technobly/parti-badge/firmware/src/music/xmassongs.h

/*
 *      Copyright 2017 Particle Industries, Inc.
 * 
 *      Originally created for the Particle Christmas Tree Shield: 
 *       https://github.com/particle-iot/xmastree. Modified to add Particle
 *      Mesh publish for netowrked light displays.
 *
 *      Licensed under the Apache License, Version 2.0 (the "License");
 *      you may not use this file except in compliance with the License.
 *      You may obtain a copy of the License at
 *
 *          http://www.apache.org/licenses/LICENSE-2.0
 *
 *      Unless required by applicable law or agreed to in writing, software
 *      distributed under the License is distributed on an "AS IS" BASIS,
 *      WITHOUT WARRANTIES OR CONDITIONS OF ANY KIND, either express or implied.
 *      See the License for the specific language governing permissions and
 *      limitations under the License.
 *
 */
#include "macros.h"

#define SONG_COUNT 5

#define SONG_JOYTOTHEWORLD 0
#define SONG_WEWHISHYOUAMERRYXMAS 1
#define SONG_RUDOLFTHEREDNOSEDREINDEER 2
#define SONG_JINGLEBELLS 3
#define SONG_SILENTNIGHT 4

#define Do 523 / 2
#define Do_ 1046 / 2
#define Re 587 / 2
#define Re_ 1175 / 2
#define Mi 659 / 2
#define Mi_ 1318 / 2
#define Fa 698 / 2
#define Fa_ 1397 / 2
#define So 784 / 2
#define La 880 / 2
#define Si 988 / 2
#define _Si 494 / 2
#define _La 440 / 2
#define _So 392 / 2

#define bt 323
#define bt2 bt * 2
#define bt3 bt * 3
#define bt6 bt * 6
#define bt1_2 bt / 2
#define bt3_2 (bt / 2) * 3
#define bt1_4 bt / 4

/*
 *      Credit:
 *          Midi to Arduino Converter
 *              - Andy Tran (extramaster), 2015
 *          https://www.extramaster.net/tools/midiToArduino/
 *
 *      The songs are generated from:
 *          https://www.extramaster.net/tools/midiToArduino/processFile/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
 *          https://www.extramaster.net/tools/midiToArduino/processFile/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
 *          https://www.extramaster.net/tools/midiToArduino/processFile/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
 *          https://www.extramaster.net/tools/midiToArduino/processFile/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
 */

/* Song List */
String songList = "Joy To The World, We Wish You A Merry Xmas, Rudolf the Red Nosed Reindeer, Jingle Bells, Silent Night";

/* An indicator to exit the current song */
bool changeSong = false;

bool delaySong(unsigned duration)
{
  while (duration > 0 && !changeSong)
  {
    unsigned thisDelay = duration > 100 ? 100 : duration;
    delay(thisDelay);
    duration -= thisDelay;
  }

  return changeSong;
}

/*
 *
 *      Silent Night
 *
 *      More Information:
 *          https://en.wikipedia.org/wiki/Silent_Night
 *
 */

#define NOTE_COUNT_SILENTNIGHT 46

const int notes_silentNight[] = {
    // Note, Duration
    So, bt3_2,
    La, bt1_2,
    So, bt,
    Mi, bt3,

    So, bt3_2,
    La, bt1_2,
    So, bt,
    Mi, bt3,

    Re_, bt2,
    Re_, bt1_2,
    Si, bt3,

    Do_, bt2,
    Do_, bt1_2,
    So, bt3,

    La, bt2,
    La, bt,
    Do_, bt3_2,
    Si, bt1_2,
    La, bt,
    So, bt3_2,
    La, bt1_2,
    So, bt,
    Mi, bt3,

    La, bt2,
    La, bt,
    Do_, bt3_2,
    Si, bt1_2,
    La, bt,
    So, bt3_2,
    La, bt1_2,
    So, bt,
    Mi, bt3,

    Re_, bt2,
    Re_, bt,
    Fa_, bt3_2,
    Re_, bt1_2,
    Si, bt,
    Do_, bt3,

    Mi_, bt3,
    Do_, bt,
    So, bt,
    Mi, bt,
    So, bt3_2,
    Fa, bt1_2,
    Re, bt,
    Do, bt6};

/*
 *
 *      Joy To The World
 *
 *      More information:
 *          https://en.wikipedia.org/wiki/Joy_to_the_World
 *
 */

#define NOTE_COUNT_JOYTOTHEWORLD 57

const float notes_joyToTheWorld[] = {
    // Note, Duration, Delay
    587,
    450.0,
    500,
    554,
    337.5,
    375,
    493,
    112.5,
    125,
    440,
    675.0,
    750,
    391,
    225.0,
    250,
    369,
    450.0,
    500,
    329,
    450.0,
    500,
    293,
    675.0,
    750.0,
    440,
    225.0,
    250.0,
    493,
    670.3125,
    744.791666667 + 5.20833333333,
    493,
    225.0,
    250.0,
    554,
    670.3125,
    744.791666667 + 5.20833333333,
    554,
    225.0,
    250.0,
    587,
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
};

/*
 *
 *      We Wish You A Merry X'mas
 *
 *      More information:
 *          https://en.wikipedia.org/wiki/We_Wish_You_a_Merry_Christmas
 *
 */

#define NOTE_COUNT_WEWISHYOUAMERRYXMAS 52

const float notes_weWishYouAMerryXmas[] = {
    // Note, Duration, Delay
    311,
    312.4995,
    347.221666667,
    415,
    312.4995,
    347.221666667,
    415,
    156.24975,
    173.610833333,
    466,
    156.24975,
    173.610833333,
    415,
    156.24975,
    173.610833333,
    391,
    156.24975,
    173.610833333,
    349,
    312.4995,
    347.221666667,
    349,
    234.374625,
    260.41625 + 86.8054166667,
    349,
    312.4995,
    347.221666667,
    466,
    312.4995,
    347.221666667,
    466,
    156.24975,
    173.610833333,
    523,
    156.24975,
    173.610833333,
    466,
    156.24975,
    173.610833333,
    415,
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
};

/*
 *
 *      Rudolf The Red Nosed Reindeer
 *
 *      More Information:
 *          https://en.wikipedia.org/wiki/Rudolph_the_Red-Nosed_Reindeer_(song)
 *
 */

#define NOTE_COUNT_RUDOLFTHEREDNOSEDREINDEER 110

const float notes_rudolfTheRedNosedReindeer[] = {
    // Note, Duration, Delay
    391,
    161.87025,
    179.855833333,
    440,
    161.87025,
    179.855833333,
    391,
    323.7405,
    359.711666667,
    329,
    323.7405,
    359.711666667,
    523,
    323.7405,
    359.711666667,
    440,
    323.7405,
    359.711666667,
    391,
    967.849203125,
    1075.38800347 + 3.74699652778,
    391,
    161.87025,
    179.855833333,
    440,
    161.87025,
    179.855833333,
    391,
    161.87025,
    179.855833333,
    440,
    161.87025,
    179.855833333,
    391,
    323.7405,
    359.711666667,
    523,
    323.7405,
    359.711666667,
    493,
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
};

/*
 *
 *      Jingle Bells
 *
 *      More information:
 *        https://en.wikipedia.org/wiki/Jingle_Bells
 *
 */

#define NOTE_COUNT_JINGLEBELLS 53

const float notes_jingleBells[] = {
    493,
    208.33275,
    231.480833333,
    493,
    208.33275,
    231.480833333,
    493,
    416.6655,
    462.961666667,
    493,
    208.33275,
    231.480833333,
    493,
    208.33275,
    231.480833333,
    493,
    416.6655,
    462.961666667,
    493,
    208.33275,
    231.480833333,
    587,
    208.33275,
    231.480833333,
    391,
    312.499125,
    347.22125,
    440,
    104.166375,
    115.740416667,
    493,
    833.331,
    925.923333333,
    523,
    208.33275,
    231.480833333,
    523,
    208.33275,
    231.480833333,
    523,
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
};

/*
 *
 *      Xmas Songs
 *
 */

void playJoyToTheWorld()
{
  int noteCount = NOTE_COUNT_JOYTOTHEWORLD;

  for (int i = 0; i < noteCount * 3; i += 3)
  {
    if (changeSong)
      return;

    Mesh.publish("tone", String(notes_joyToTheWorld[i]));
    tone(BUZZER_PIN, notes_joyToTheWorld[i], notes_joyToTheWorld[i + 1]);
    delay(notes_joyToTheWorld[i + 2]);
    Mesh.publish("no-tone", NULL);
  }
}

void playWeWishYouAMerryXmas()
{
  int noteCount = NOTE_COUNT_WEWISHYOUAMERRYXMAS;

  for (int i = 0; i < noteCount * 3; i += 3)
  {
    if (changeSong)
      return;

    Mesh.publish("tone", String(notes_weWishYouAMerryXmas[i]));
    tone(BUZZER_PIN, notes_weWishYouAMerryXmas[i], notes_weWishYouAMerryXmas[i + 1]);
    delay(notes_weWishYouAMerryXmas[i + 2]);
    Mesh.publish("no-tone", NULL);
  }
}

void playRudolfTheRedNosedReindeer()
{
  int noteCount = NOTE_COUNT_RUDOLFTHEREDNOSEDREINDEER;

  for (int i = 0; i < noteCount * 3; i += 3)
  {
    if (changeSong)
      return;

    Mesh.publish("tone", String(notes_rudolfTheRedNosedReindeer[i]));
    tone(BUZZER_PIN, notes_rudolfTheRedNosedReindeer[i], notes_rudolfTheRedNosedReindeer[i + 1]);
    delay(notes_rudolfTheRedNosedReindeer[i + 2]);
    Mesh.publish("no-tone", NULL);
  }
}

void playJingleBells()
{
  int noteCount = NOTE_COUNT_JINGLEBELLS;

  for (int i = 0; i < noteCount * 3; i += 3)
  {
    if (changeSong)
      return;

    Mesh.publish("tone", String(notes_jingleBells[i]));
    tone(BUZZER_PIN, notes_jingleBells[i], notes_jingleBells[i + 1]);
    delay(notes_jingleBells[i + 2]);
    Mesh.publish("no-tone", NULL);
  }
}

void playSilentNight()
{
  int noteCount = NOTE_COUNT_SILENTNIGHT;

  for (int i = 0; i < noteCount * 2; i += 2)
  {
    if (changeSong)
      return;

    Mesh.publish("tone", String(notes_jingleBells[i]));
    tone(BUZZER_PIN, notes_jingleBells[i], notes_silentNight[i + 1]);
    delay(notes_silentNight[i + 1] * 1.3);
    Mesh.publish("no-tone", NULL);
  }
}
