technobly/parti-badge/firmware/src/images/battery.h

static const unsigned char batteryFullImage[] =
{
0B00111111,0B11111111,0B11111111,0B11111111,0B11111111,0B11111111,0B11111111,0B11111100,0B00000000
,0B01111111,0B11111111,0B11111111,0B11111111,0B11111111,0B11111111,0B11111111,0B11111110,0B00000000
,0B11111111,0B11111111,0B11111111,0B11111111,0B11111111,0B11111111,0B11111111,0B11111111,0B00000000
,0B11111111,0B11111111,0B11111111,0B11111111,0B11111111,0B11111111,0B11111111,0B11111111,0B00000000
,0B11110000,0B00000000,0B00000000,0B00000000,0B00000000,0B00000000,0B00000000,0B00001111,0B00000000
,0B11110000,0B00000000,0B00000000,0B00000000,0B00000000,0B00000000,0B00000000,0B00001111,0B00000000
,0B11110000,0B00000000,0B00000000,0B00000000,0B00000000,0B00000000,0B00000000,0B00001111,0B11111100
,0B11110000,0B00000000,0B00000000,0B00000000,0B00000000,0B00000000,0B00000000,0B00001111,0B11111110
,0B11110000,0B11111111,0B11111111,0B11001111,0B11111111,0B11000111,0B11111111,0B00001111,0B11111111
,0B11110000,0B11111111,0B11111111,0B11001111,0B11111111,0B11000111,0B11111111,0B00001111,0B11111111
,0B11110000,0B11111111,0B11111111,0B10011111,0B11111111,0B11001111,0B11111111,0B00001111,0B00001111
,0B11110000,0B11111111,0B11111111,0B10111111,0B11111111,0B11011111,0B11111111,0B00001111,0B00001111
,0B11110000,0B11111111,0B11111111,0B00111111,0B11111111,0B10011111,0B11111111,0B00001111,0B00001111
,0B11110000,0B11111111,0B11111111,0B00111111,0B11111111,0B10111111,0B11111111,0B00001111,0B00001111
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
,0B01111111,0B11111111,0B11111111,0B11111111,0B11111111,0B11111111,0B11111111,0B11111110,0B00000000
,0B00111111,0B11111111,0B11111111,0B11111111,0B11111111,0B11111111,0B11111111,0B11111100,0B00000000
};
