technobly/parti-badge/firmware/src/images/spectra.h

static const unsigned char spectraLogo[] =
{
0B00000000,0B00000000,0B00000000,0B00000000,0B00000000,0B00000000,0B00000000,0B00000000,0B00000000,0B00000000,0B00000000,0B00000000,0B00000000,0B00000000,0B00000000,0B00000000
,0B00000000,0B00000000,0B00000000,0B00000000,0B00000000,0B00000000,0B00000000,0B00000000,0B00000000,0B00000000,0B00000000,0B00000000,0B00000000,0B00000000,0B00000000,0B00000000
,0B00000000,0B00000000,0B00000000,0B00000000,0B00000000,0B00000000,0B00000000,0B00000000,0B00000000,0B00000000,0B00000000,0B00000000,0B00000000,0B00000000,0B00000000,0B00000000
,0B00000000,0B00000000,0B00000000,0B00000000,0B00000000,0B00000000,0B00000000,0B00000000,0B00000000,0B00000000,0B00000000,0B00000000,0B00000000,0B00000000,0B00000000,0B00000000
,0B00000000,0B00000000,0B00000000,0B00000000,0B00000000,0B00000000,0B00000000,0B00000000,0B00000000,0B00000000,0B00000000,0B00000000,0B00000000,0B00000000,0B00000000,0B00000000
,0B00000000,0B00000000,0B00000000,0B00000000,0B00000000,0B00000000,0B00000000,0B00000000,0B00000000,0B00000000,0B00000000,0B00000000,0B00000000,0B00000000,0B00000000,0B00000000
,0B00000000,0B00000000,0B00000000,0B00000000,0B00000000,0B00000000,0B00000000,0B00000000,0B00000000,0B00000000,0B00000000,0B00000000,0B00000000,0B00000000,0B00000000,0B00000000
,0B00000000,0B00000000,0B00000000,0B00000000,0B00000000,0B00000000,0B00000000,0B00000000,0B00000000,0B00000000,0B00000000,0B00000000,0B00000000,0B00000000,0B00000000,0B00000000
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
,0B00000000,0B00000000,0B00000000,0B00000000,0B00010000,0B01000000,0B00000000,0B00100000,0B01000000,0B00000000,0B00000100,0B00010000,0B00000000,0B00000000,0B00000000,0B00000000
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
};
