technobly/parti-badge/firmware/src/images/konami.h

static const unsigned char konamiLogo[] =
{
0B00000000,0B00000000,0B00000000,0B00000000,0B00000000,0B00000000,0B00000000,0B00000000,0B00000000,0B00000000,0B00000000,0B00000000,0B00000000,0B00000000,0B00000000,0B00000000
,0B00000000,0B00000000,0B00000000,0B00000000,0B00000000,0B00000000,0B00000000,0B00000000,0B00000000,0B00000000,0B00000000,0B00000000,0B00000000,0B00000000,0B00000000,0B00000000
,0B00000000,0B00000000,0B00000000,0B00000000,0B00000000,0B00000000,0B00000000,0B00000000,0B11111111,0B11111111,0B00000000,0B00000000,0B00000000,0B00000000,0B00000000,0B00000000
,0B00000000,0B00000000,0B00000000,0B00000000,0B00000000,0B00000000,0B00000000,0B00000001,0B11111111,0B11111111,0B00000000,0B00000000,0B00000000,0B00000000,0B00000000,0B00000000
,0B00000000,0B00000000,0B00000000,0B00000000,0B00000000,0B00000000,0B00000000,0B00000001,0B11111111,0B11111110,0B00000000,0B00000000,0B00000000,0B00000000,0B00000000,0B00000000
,0B00000000,0B00000000,0B00000000,0B00000000,0B00000000,0B00000000,0B00000000,0B00000001,0B11111111,0B11111110,0B00000000,0B00000000,0B00000000,0B00000000,0B00000000,0B00000000
,0B00000000,0B00000000,0B00000000,0B00000000,0B00000000,0B00000000,0B00000000,0B00000011,0B11111111,0B11111110,0B00000000,0B00000000,0B00000000,0B00000000,0B00000000,0B00000000
,0B00000000,0B00000000,0B00000000,0B00000000,0B00000000,0B00000000,0B00000000,0B00000011,0B11111111,0B11111100,0B00000000,0B00000000,0B00000000,0B00000000,0B00000000,0B00000000
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
,0B00000000,0B00000000,0B00000000,0B00000000,0B00000000,0B00000000,0B00011111,0B11111111,0B11100000,0B00000000,0B00000000,0B00000000,0B00000000,0B00000000,0B00000000,0B00000000
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
};
