technobly/parti-badge/firmware/src/images/spark.h

static const unsigned char sparkLogo[] =
{
 0B00000000,0B00000000,0B00000000,0B00000000,0B00000000,0B00000000,0B00000000,0B00000000,0B00000000,0B00000000,0B00000000,0B00000000,0B00000000,0B00000000,0B00000000,0B00000000
,0B00000000,0B00000000,0B00000000,0B00000000,0B00000000,0B00000000,0B00000000,0B00000000,0B00000000,0B00000000,0B00000000,0B00000000,0B00000000,0B00000000,0B00000000,0B00000000
,0B00000000,0B00000000,0B00000000,0B00000000,0B00000000,0B00000000,0B00000000,0B00000001,0B10000000,0B00000000,0B00000000,0B00000000,0B00000000,0B00000000,0B00000000,0B00000000
,0B00000000,0B00000000,0B00000000,0B00000000,0B00000000,0B00000000,0B00000000,0B00000001,0B10000000,0B00000000,0B00000000,0B00000000,0B00000000,0B00000000,0B00000000,0B00000000
,0B00000000,0B00000000,0B00000000,0B00000000,0B00000000,0B00000000,0B00000000,0B00000001,0B10000000,0B00000000,0B00000000,0B00000000,0B00000000,0B00000000,0B00000000,0B00000000
,0B00000000,0B00000000,0B00000000,0B00000000,0B00000000,0B00000000,0B00000000,0B00000001,0B10000000,0B00000000,0B00000000,0B00000000,0B00000000,0B00000000,0B00000000,0B00000000
,0B00000000,0B00000000,0B00000000,0B00000000,0B00000000,0B00000000,0B00000000,0B00000001,0B10000000,0B00000000,0B00000000,0B00000000,0B00000000,0B00000000,0B00000000,0B00000000
,0B00000000,0B00000000,0B00000000,0B00000000,0B00000000,0B00000001,0B00000000,0B00000011,0B11000000,0B00000000,0B10000000,0B00000000,0B00000000,0B00000000,0B00000000,0B00000000
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
,0B00000000,0B00000000,0B00000000,0B00000000,0B00000000,0B00000000,0B10000000,0B00000011,0B11000000,0B00000001,0B00000000,0B00000000,0B00000000,0B00000000,0B00000000,0B00000000
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

};
