technobly/parti-badge/firmware/src/music/music.h

#ifndef PARTICLE_MUSIC_H
#define PARTICLE_MUSIC_H

void playTones(int tonePin, const int tones[]);
void playStartup(int tonePin, bool lightLEDs);
void playGameOver(int tonePin, bool lightLEDs);
void playBeegees();
void buzz_sound(int buzz_length_ms, int buzz_delay_us);

#endif
