technobly/parti-badge/firmware/src/parti-badge.h

/* Display Mode macros */
#define DISPLAY_MODE 1
#define GAME_MODE 2

/* Piezo Pin */
#define BUZZER_PIN TX

/* IR Receiver PIN */
#define IR_RECEIVER_PIN RX

/* Tactile LED Button Pins */
/* LEDS */
#define RED_LED A3
#define GREEN_LED A2
#define BLUE_LED A1
#define YELLOW_LED A0
/* Buttons */
#define RED_BUTTON_A WKP
#define BLUE_BUTTON_B A5
#define GREEN_BUTTON_C DAC
#define YELLOW_BUTTON_D A4

/* Joystick Buttons */
#define JOYSTICK_UP D6
#define JOYSTICK_DOWN D5
#define JOYSTICK_LEFT D4
#define JOYSTICK_RIGHT D3
#define JOYSTICK_CENTER D2

/* General Macros */
#define TEMP_CHECK_INTERVAL 120000
#define DEBOUNCE_INTERVAL 10
