technobly/parti-badge/firmware/src/images/mesh.h

static const unsigned char meshLogo[] = {
0B00000000,0B00111111,0B11111111,0B11111000,0B00000000,0B00000000,0B00000000,0B00000000
,0B00000000,0B01111111,0B11111111,0B11111100,0B00000000,0B00000000,0B00000000,0B00000000
,0B00000000,0B01111111,0B11111111,0B11111100,0B00000000,0B00000000,0B00000000,0B00000000
,0B00000000,0B11111111,0B11111111,0B11111100,0B00000000,0B00000000,0B00000000,0B00000000
,0B00000001,0B11100000,0B00000000,0B00001110,0B00000000,0B00000000,0B00000000,0B00000000
,0B00000001,0B11100000,0B00000000,0B00001110,0B00000000,0B00000000,0B00000000,0B00000000
,0B00000011,0B11000000,0B00000000,0B00000111,0B10000000,0B00000000,0B00000000,0B00000000
,0B00000011,0B11000000,0B00000000,0B00000111,0B10000000,0B00000000,0B00000000,0B00000000
,0B00000111,0B10000000,0B00000000,0B00000011,0B11000000,0B00000000,0B00000000,0B00000000
,0B00000111,0B10000000,0B00000000,0B00000011,0B11000000,0B00000000,0B00000000,0B00000000
,0B00001111,0B00000000,0B00000000,0B00000011,0B11000000,0B00000000,0B00000000,0B00000000
,0B00011110,0B00000000,0B00000000,0B00000001,0B11100000,0B00000000,0B00000000,0B00000000
,0B00011110,0B00000000,0B00000000,0B00000001,0B11100000,0B00000000,0B00000000,0B00000000
,0B00111100,0B00000000,0B00000000,0B00000000,0B01110000,0B00000000,0B00000000,0B00000000
,0B00111100,0B00000000,0B00000000,0B00000000,0B01111000,0B00000000,0B00000000,0B00000000
,0B01111000,0B00000000,0B00000000,0B00000000,0B00111111,0B11111111,0B11111100,0B00000000
,0B11110000,0B00000000,0B00000000,0B00000000,0B00111111,0B11111111,0B11111110,0B00000000
,0B11110000,0B00000000,0B00000000,0B00000000,0B00111111,0B11111111,0B11111111,0B00000000
,0B01111000,0B00000000,0B00000000,0B00000000,0B00111111,0B11111111,0B11111111,0B00000000
,0B01111000,0B00000000,0B00000000,0B00000000,0B00111000,0B00000000,0B00000111,0B10000000
,0B00111100,0B00000000,0B00000000,0B00000000,0B01110000,0B00000000,0B00000111,0B10000000
,0B00011110,0B00000000,0B00000000,0B00000001,0B11110000,0B00000000,0B00000011,0B11000000
,0B00011110,0B00000000,0B00000000,0B00000001,0B11100000,0B00000000,0B00000001,0B11100000
,0B00001111,0B00000000,0B00000000,0B00000011,0B11000000,0B00000000,0B00000001,0B11100000
,0B00001111,0B00000000,0B00000000,0B00000011,0B11000000,0B00000000,0B00000000,0B11110000
,0B00000011,0B11000000,0B00000000,0B00000011,0B11000000,0B00000000,0B00000000,0B01111000
,0B00000011,0B11000000,0B00000000,0B00000011,0B11000000,0B00000000,0B00000000,0B01111000
,0B00000011,0B11000000,0B00000000,0B00000111,0B10000000,0B00000000,0B00000000,0B01111100
,0B00000001,0B11100000,0B00000000,0B00001110,0B00000000,0B00000000,0B00000000,0B00111100
,0B00000000,0B11111111,0B11111111,0B11111100,0B00000000,0B00000000,0B00000000,0B00011110
,0B00000000,0B11111111,0B11111111,0B11111100,0B00000000,0B00000000,0B00000000,0B00001111
,0B00000000,0B01111111,0B11111111,0B11111100,0B00000000,0B00000000,0B00000000,0B00001111
,0B00000000,0B01111111,0B11111111,0B11111100,0B00000000,0B00000000,0B00000000,0B00001111
,0B00000000,0B11111111,0B11111111,0B11111100,0B00000000,0B00000000,0B00000000,0B00011110
,0B00000001,0B11100000,0B00000000,0B00001110,0B00000000,0B00000000,0B00000000,0B00111100
,0B00000011,0B11000000,0B00000000,0B00000111,0B10000000,0B00000000,0B00000000,0B00111100
,0B00000011,0B11000000,0B00000000,0B00000111,0B10000000,0B00000000,0B00000000,0B01111000
,0B00000011,0B11000000,0B00000000,0B00000111,0B10000000,0B00000000,0B00000000,0B01111000
,0B00000111,0B10000000,0B00000000,0B00000011,0B11000000,0B00000000,0B00000000,0B11110000
,0B00001111,0B00000000,0B00000000,0B00000011,0B11000000,0B00000000,0B00000001,0B11100000
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
};
