technobly/parti-badge/firmware/src/images/humidity.h

static const unsigned char humidityImage[] =
{
  0B00000000,0B01100000,0B00000000
  ,0B00000000,0B01100000,0B00000000
  ,0B00000000,0B11110000,0B00000000
  ,0B00000001,0B11111000,0B00000000
  ,0B00000011,0B11111100,0B00000000
  ,0B00000011,0B11111100,0B00000000
  ,0B00000111,0B11111110,0B00000000
  ,0B00001111,0B11111111,0B00000000
  ,0B00011111,0B11111111,0B10000000
  ,0B00011111,0B11111111,0B10000000
  ,0B00111100,0B01111111,0B11000000
  ,0B00111000,0B00111111,0B11000000
  ,0B01111001,0B00111001,0B11100000
  ,0B01111000,0B00110001,0B11100000
  ,0B11111100,0B01100011,0B11110000
  ,0B11111111,0B11000111,0B11110000
  ,0B11111111,0B10001111,0B11110000
  ,0B11111111,0B00011111,0B11110000
  ,0B11111110,0B00111111,0B11110000
  ,0B11111100,0B01100011,0B11110000
  ,0B01111000,0B11001001,0B11100000
  ,0B01111001,0B11001001,0B11100000
  ,0B00111111,0B11000001,0B11000000
  ,0B00111111,0B11110111,0B11000000
  ,0B00011111,0B11111111,0B10000000
  ,0B00000111,0B11111110,0B00000000
  ,0B00000001,0B11111000,0B00000000
};
