technobly/parti-badge/firmware/src/images/temp.h

static const unsigned char tempImage[] =
{
0B00000011,0B11000000
,0B00001111,0B11110000
,0B00011110,0B01111000
,0B00011000,0B00011000
,0B00111000,0B00011100
,0B00111000,0B00011100
,0B00111000,0B00011100
,0B00111000,0B00011100
,0B00111000,0B00011100
,0B00111000,0B00011100
,0B00111000,0B00011100
,0B00111000,0B00011100
,0B00111000,0B00011100
,0B00111000,0B00011100
,0B00111000,0B00011100
,0B00111000,0B00011100
,0B00111000,0B00011100
,0B00111000,0B00011100
,0B00111000,0B00011100
,0B00111000,0B00011100
,0B00111000,0B00011100
,0B00111000,0B00011100
,0B00111000,0B00011100
,0B00111000,0B00011100
,0B00111000,0B00011100
,0B00111000,0B00011100
,0B00111111,0B11111100
,0B00111111,0B11111100
,0B00111111,0B11111100
,0B00111111,0B11111100
,0B01111111,0B11111110
,0B01111111,0B11111110
,0B11111111,0B11111111
,0B11111111,0B11111111
,0B11111111,0B11111111
,0B11111111,0B11111111
,0B11111111,0B11111111
,0B11111111,0B11111111
,0B01111111,0B11111110
,0B01111111,0B11111110
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
};
